adamarthurryan/moskotron/adsr and vca/top.png

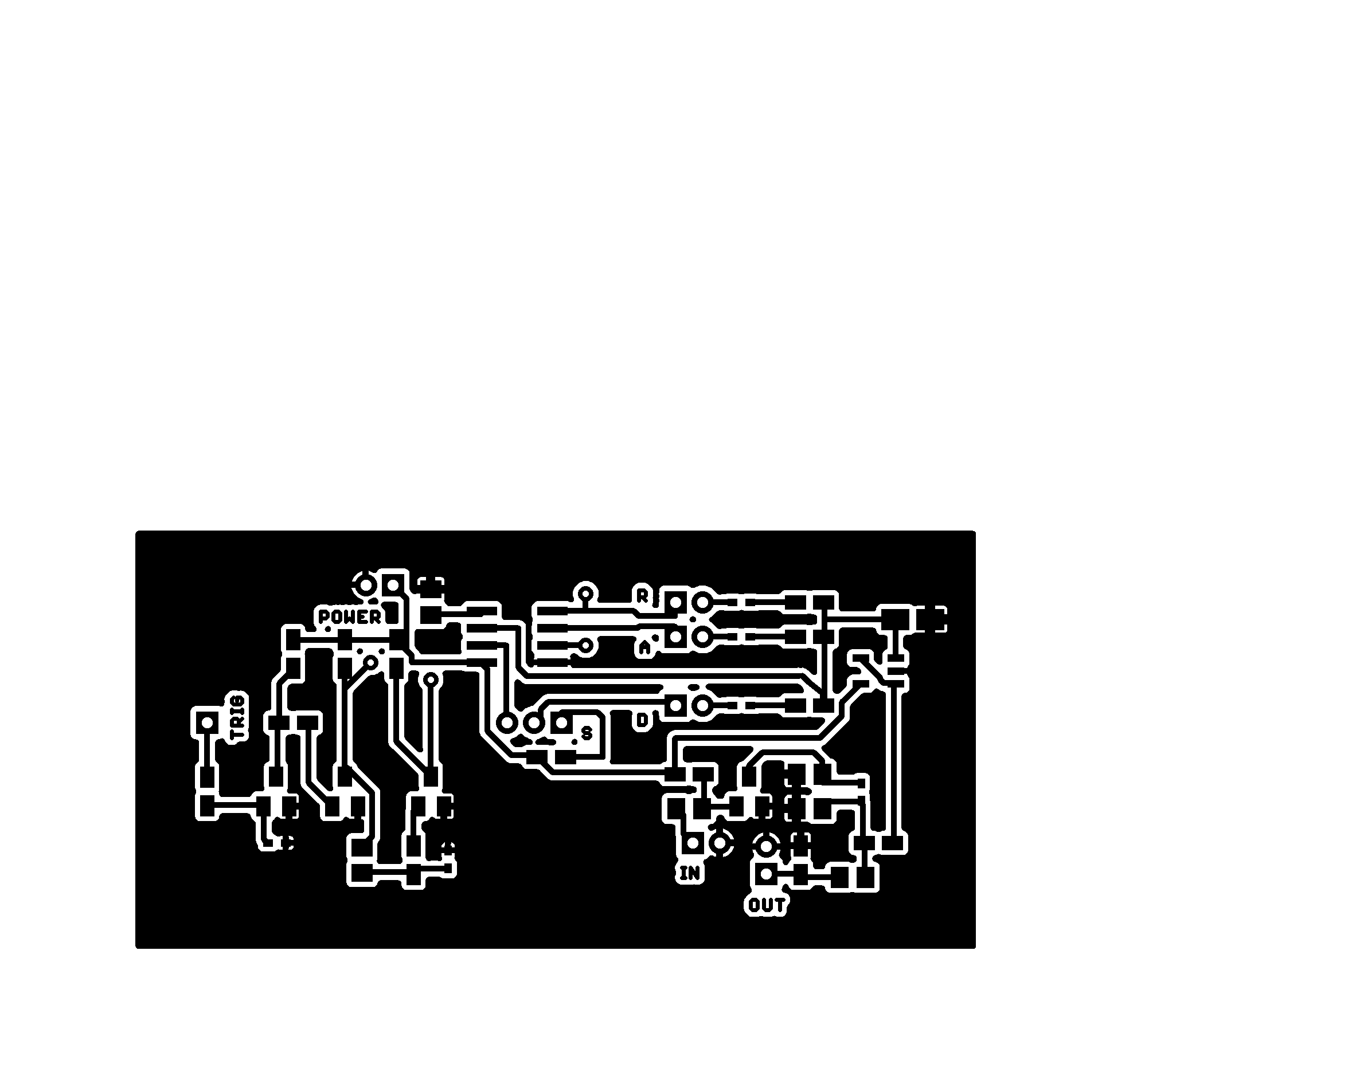
adsr and vca/top.png
