adamarthurryan/moskotron/documentation/adam playing - small.jpg

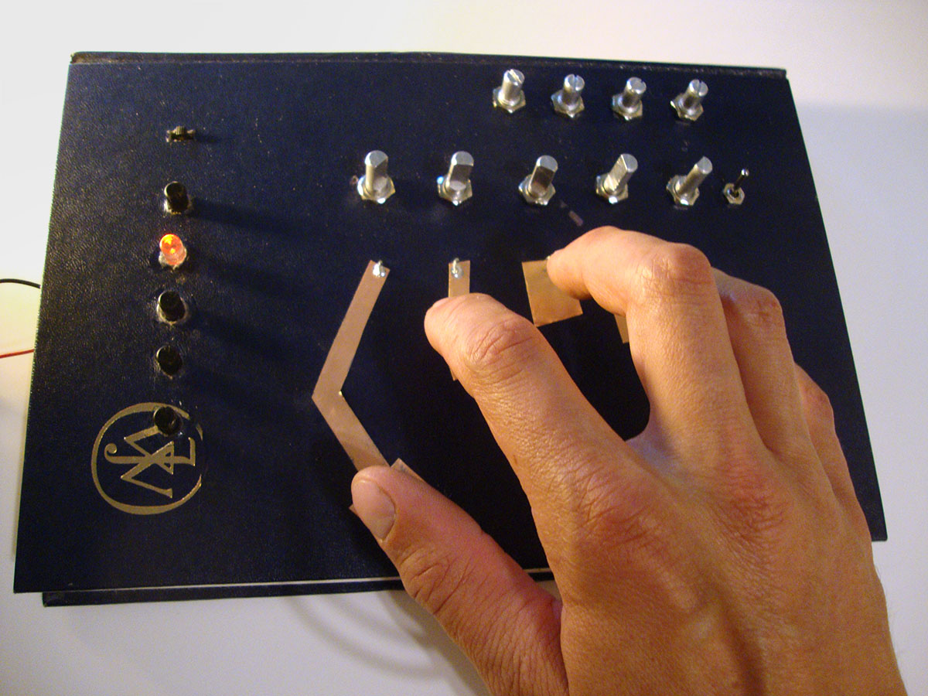
documentation/adam playing - small.jpg
