adamarthurryan/moskotron/documentation/adsr board.png

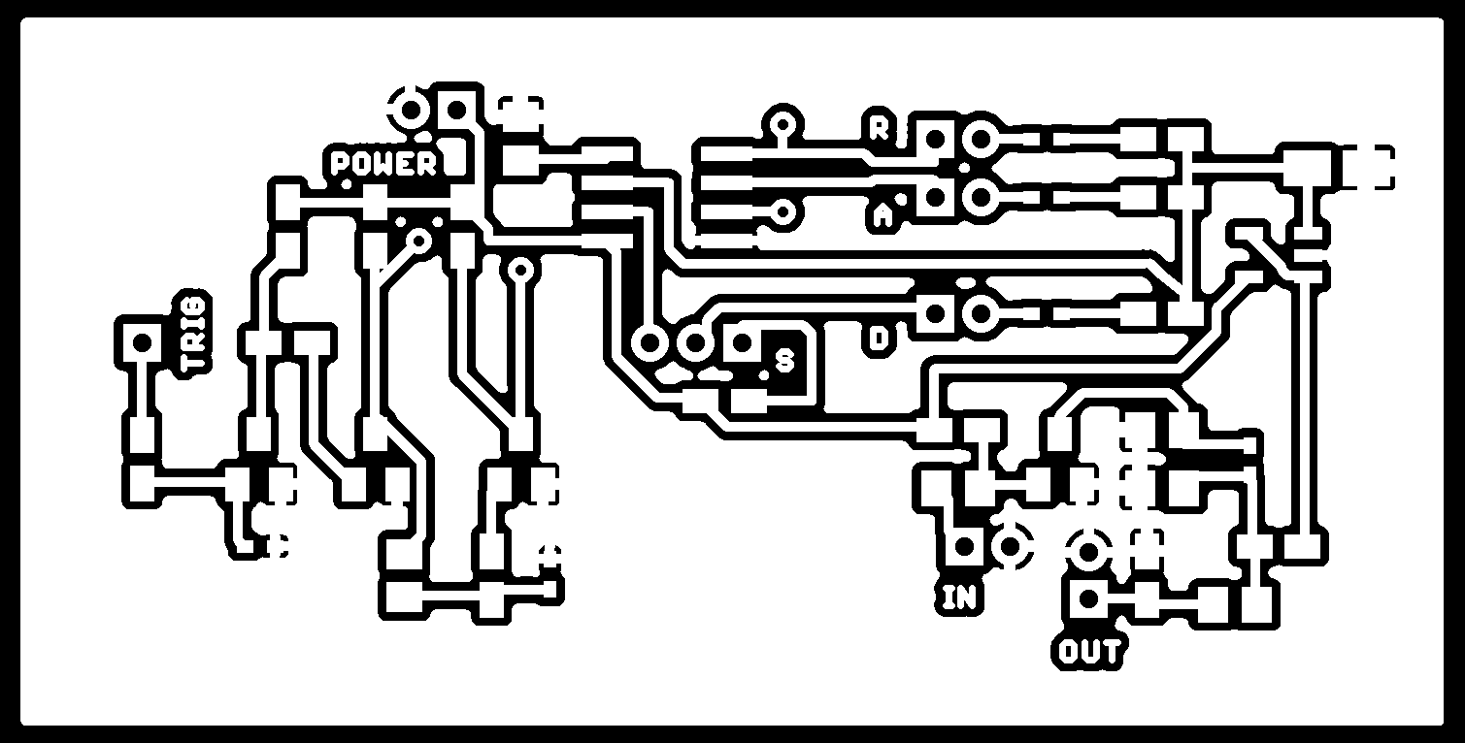
documentation/adsr board.png
