adamarthurryan/moskotron/documentation/book open - small.jpg

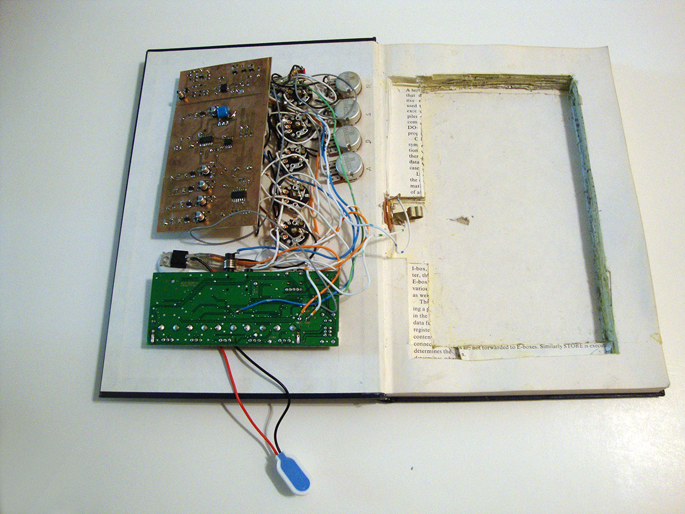
documentation/book open - small.jpg
