adamarthurryan/moskotron/documentation/pitch input board.png

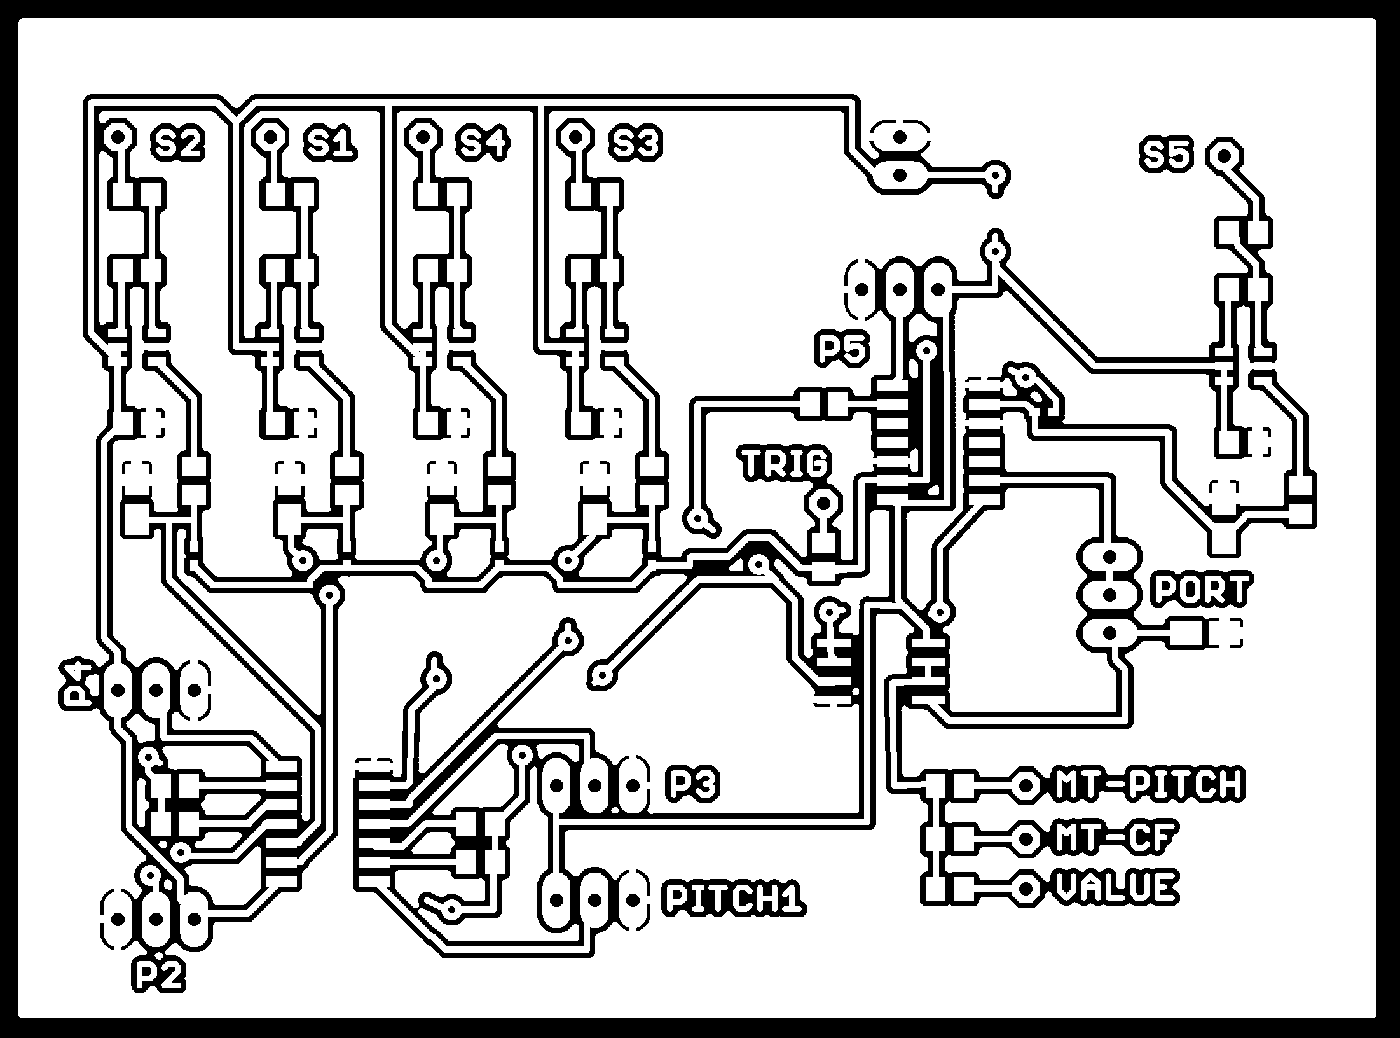
documentation/pitch input board.png
