adamarthurryan/moskotron/pitch input/placement.png

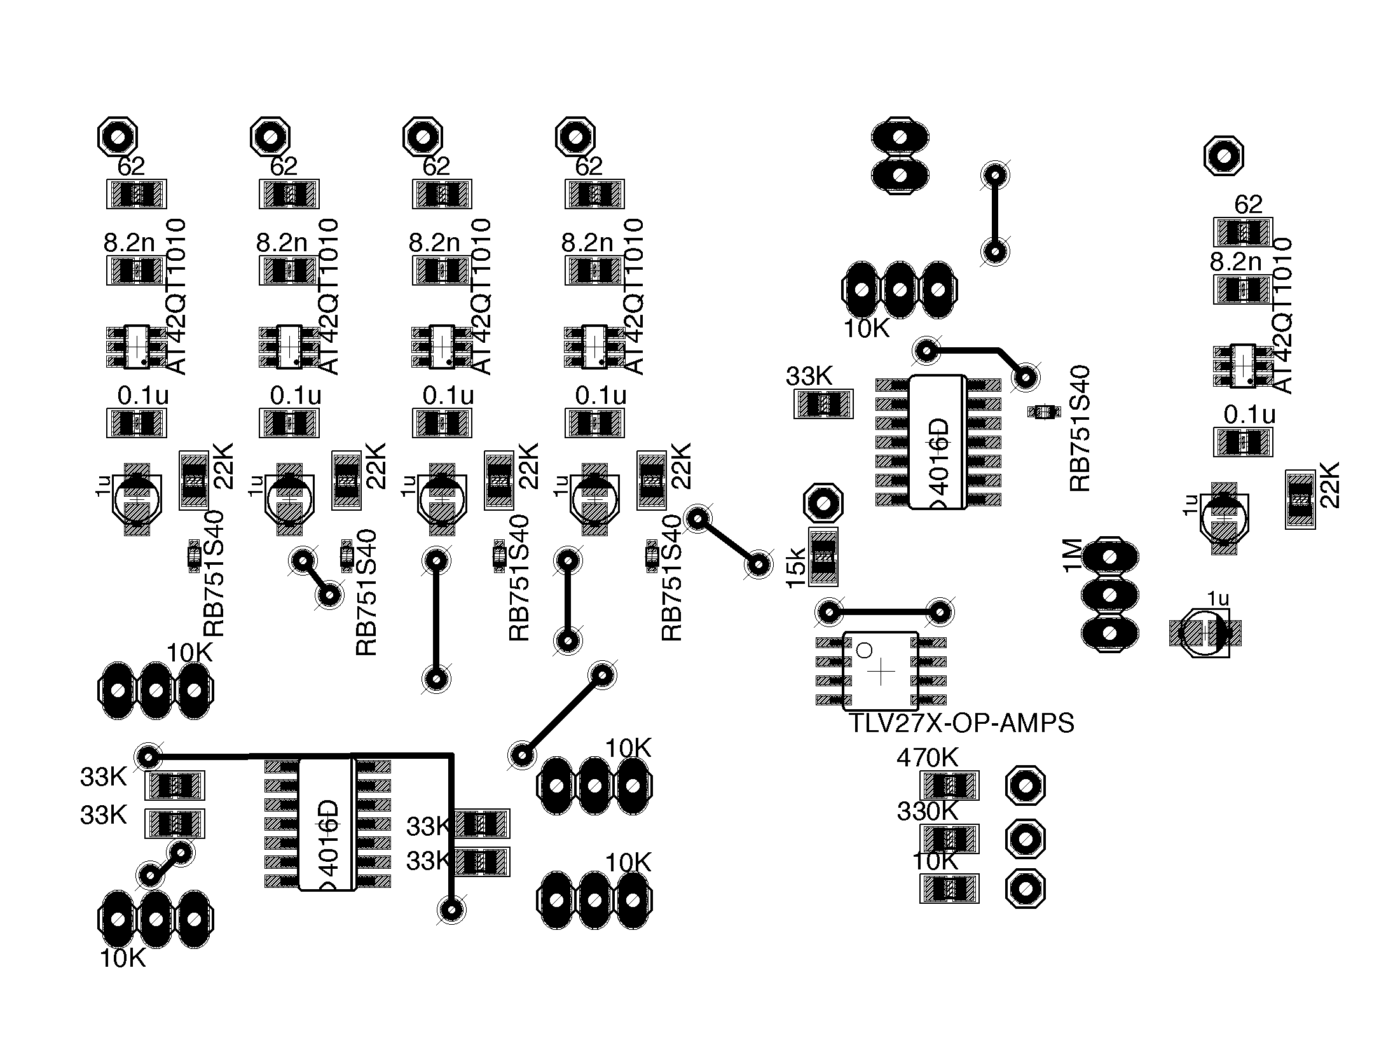
pitch input/placement.png
